evangehler/SwampSynth/hardware/swampthing.kicad_sch

## KiCad design hardware/swampthing.kicad_sch (2025-10-20, an earlier design)

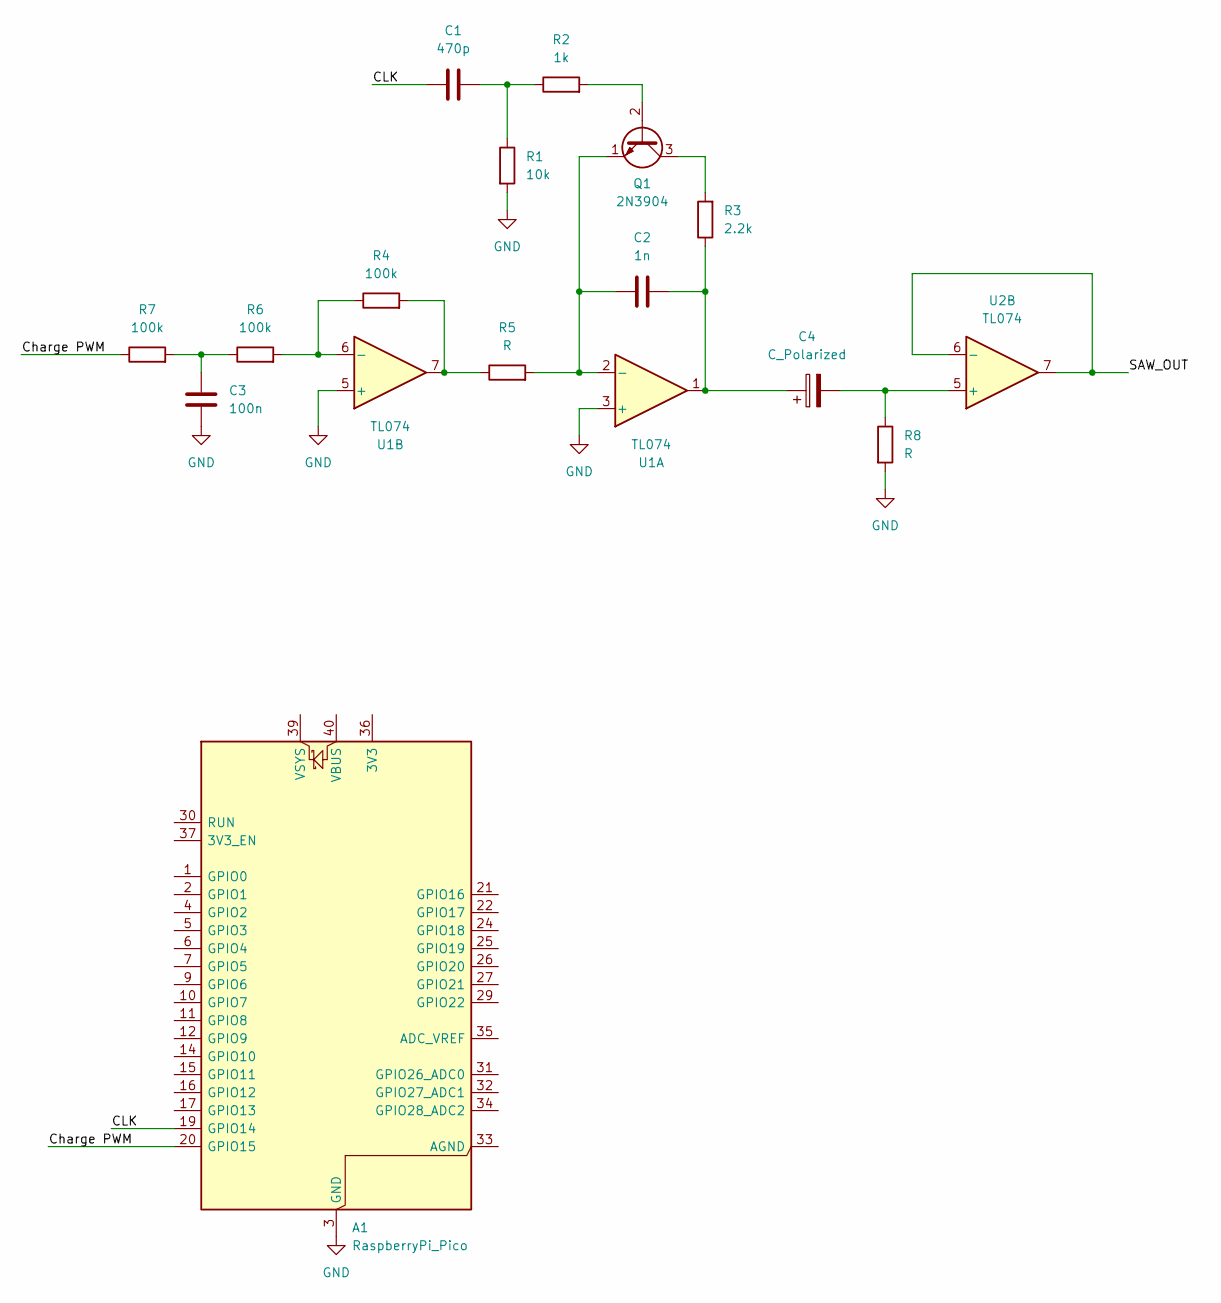
[picture p3: schematic swampthing.kicad_sch]

Parts:
A1: RaspberryPi_Pico; RaspberryPi_Pico_Common_Unspecified
C1: 470p
C2: 1n
C3: 100n
C4: C_Polarized
Q1: 2N3904; TO-92_Inline
R1: 10k
R2: 1k
R3: 2.2k
R4, R6, R7: 100k
R5, R8: R
U1: TL074; DIP-14_W7.62mm
U2: TL074

Connections:
CLK: A1.19 (GPIO14), C1.1
Charge PWM: A1.20 (GPIO15), R7.1
GND: A1.3 (GND), A1.8 (GND), A1.13 (GND), A1.18 (GND), A1.23 (GND), A1.28 (GND), A1.38 (GND), C3.2, R1.2, R8.2, U1.3 (+), U1.5 (+)
unnamed: C1.2, R1.1, R2.1
unnamed: C2.1, Q1.1 (E), R5.2, U1.2 (-)
unnamed: C2.2, C4.1, R3.1, U1.1
unnamed: C3.1, R6.1, R7.2
unnamed: C4.2, R8.1, U2.5 (+)
unnamed: Q1.2 (B), R2.2
unnamed: Q1.3 (C), R3.2
unnamed: R4.1, R6.2, U1.6 (-)
unnamed: R4.2, R5.1, U1.7
SAW_OUT: U2.6 (-), U2.7
